TrojanPinata/Model-B/assets/keymap.png

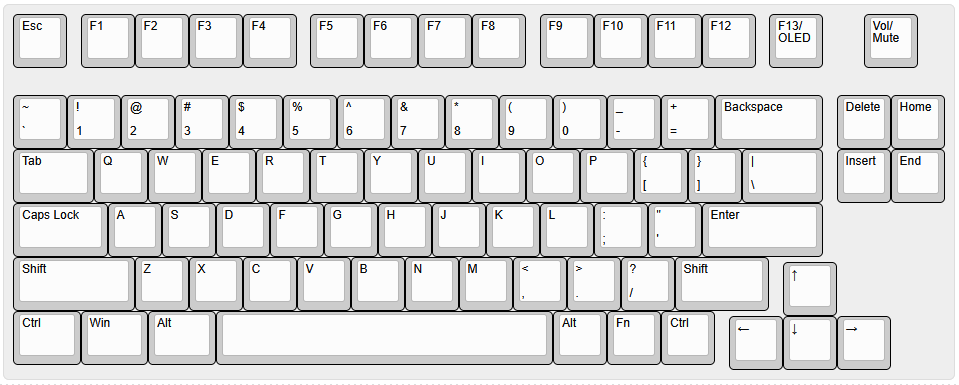
assets/keymap.png
