TrojanPinata/Model-B/assets/modelb.png

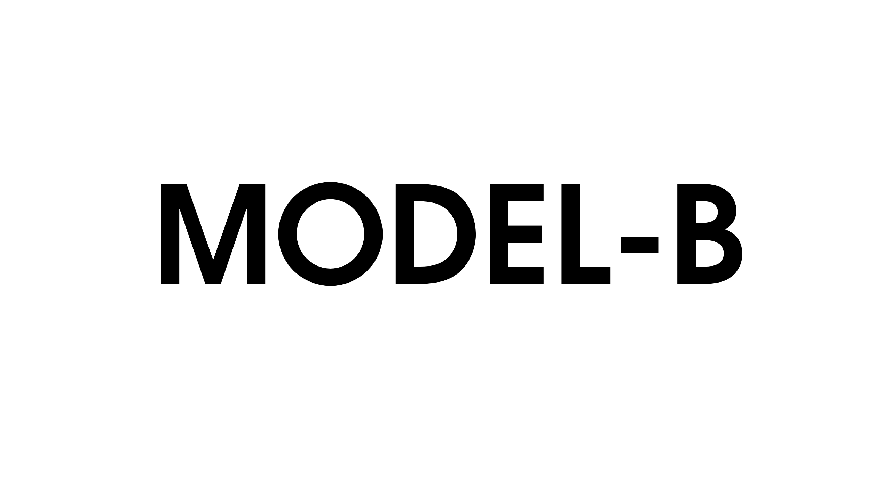
assets/modelb.png
