TrojanPinata/Model-B/case/blk.png

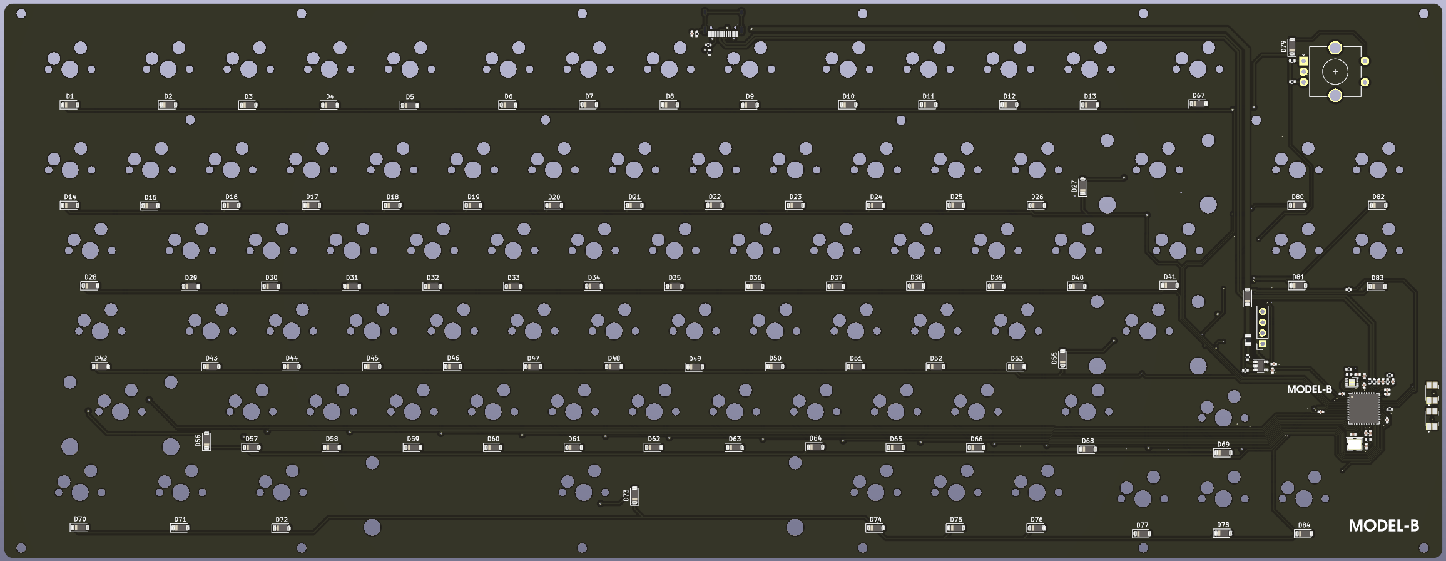
case/blk.png
