TrojanPinata/Model-B/case/blk_rear.png

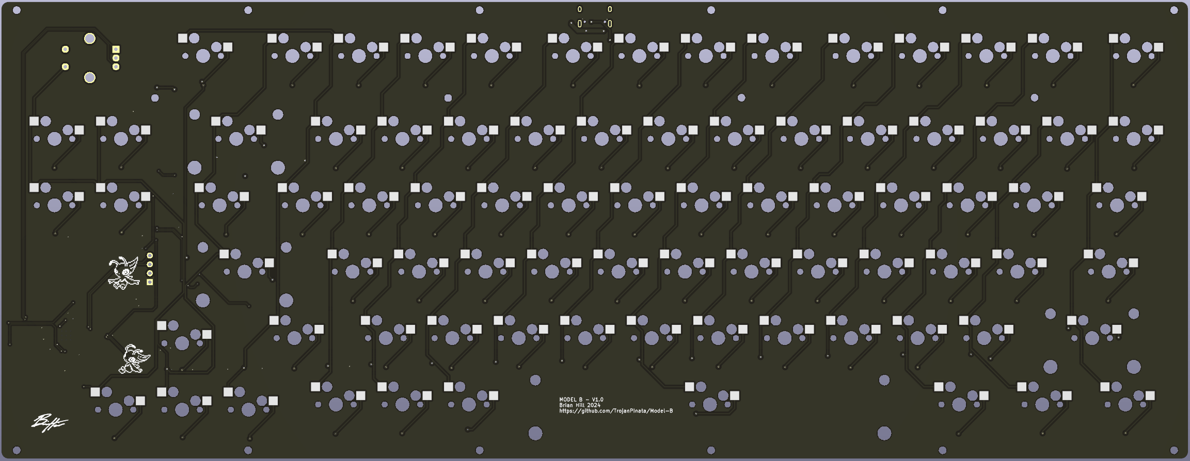
case/blk_rear.png
