TrojanPinata/Model-B/case/board.png

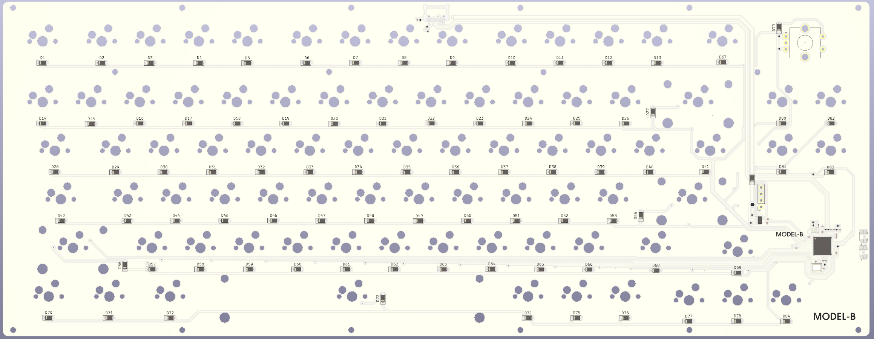
case/board.png
