TrojanPinata/Model-B/case/rear.png

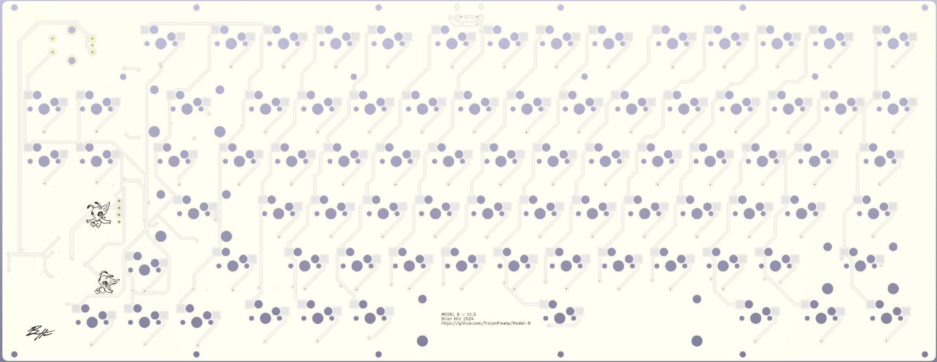
case/rear.png
