TrojanPinata/Model-B/case/ref-trans.png

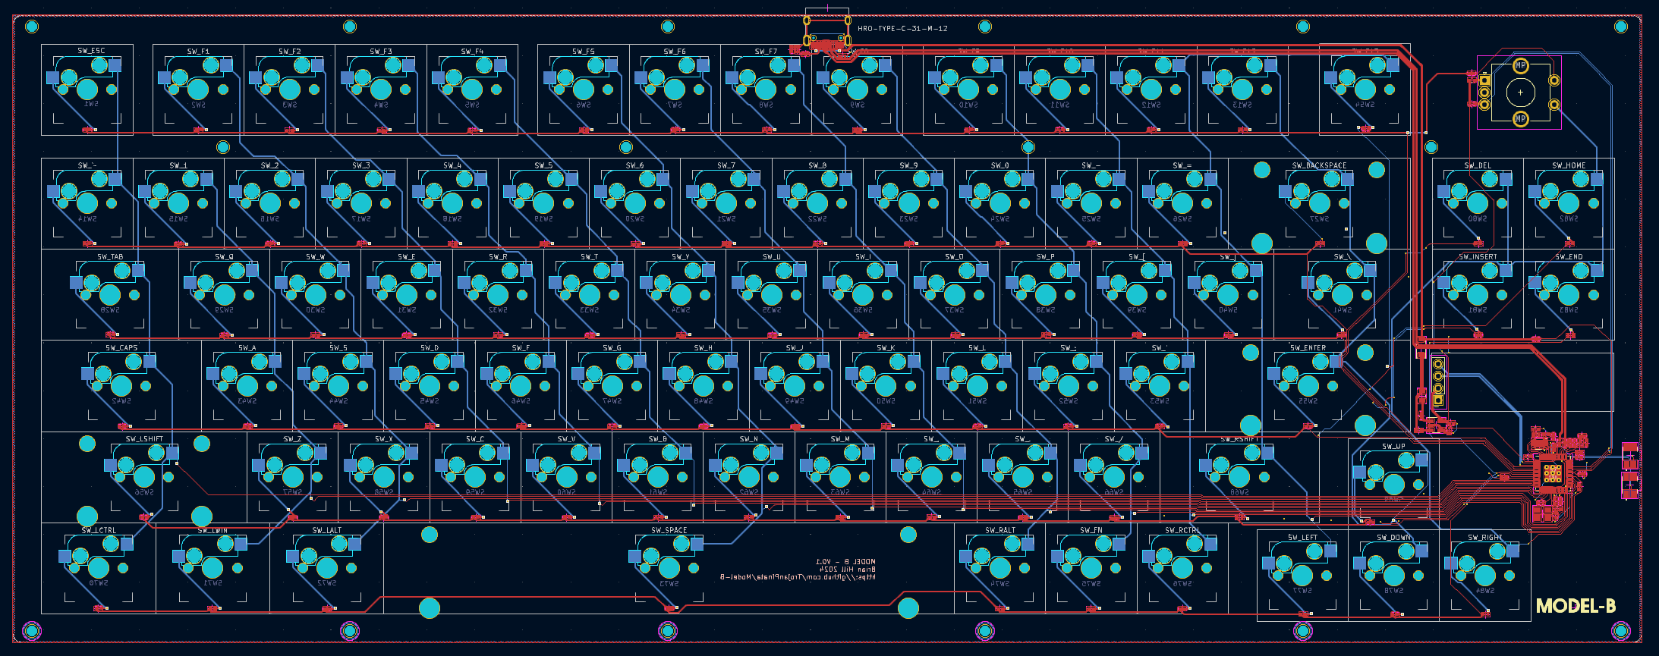
case/ref-trans.png
