TrojanPinata/Model-B/case/ref.png

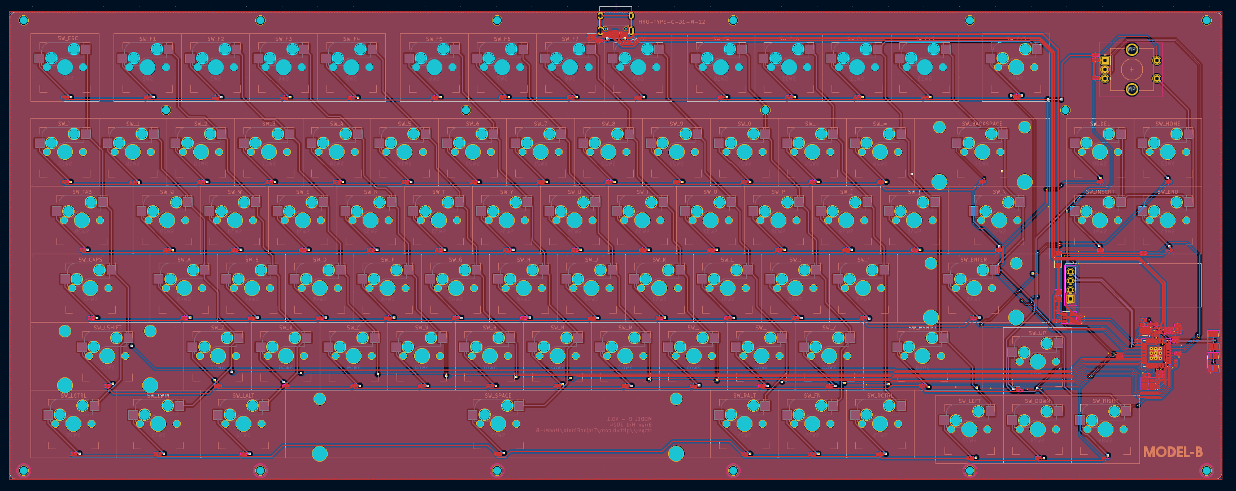
case/ref.png
