TrojanPinata/Model-B/case/renders/keyb2.png

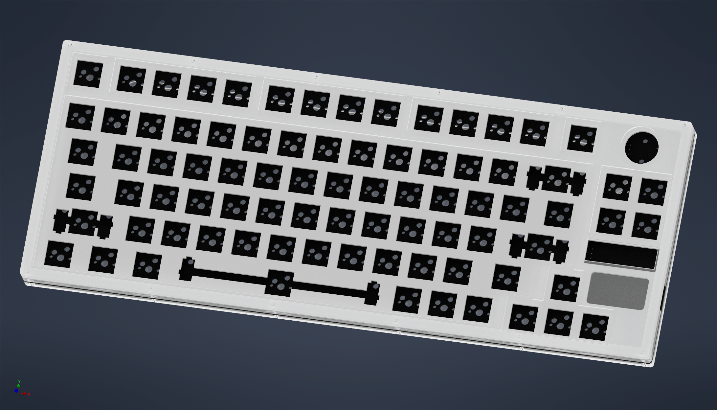
case/renders/keyb2.png
