TrojanPinata/Model-B/case/renders/keyb3.png

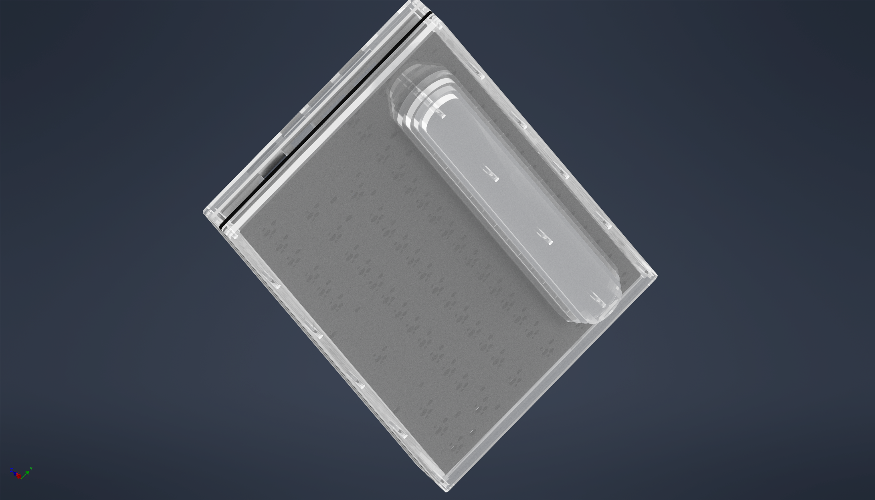
case/renders/keyb3.png
