TrojanPinata/Model-B/case/renders/keyb4.png

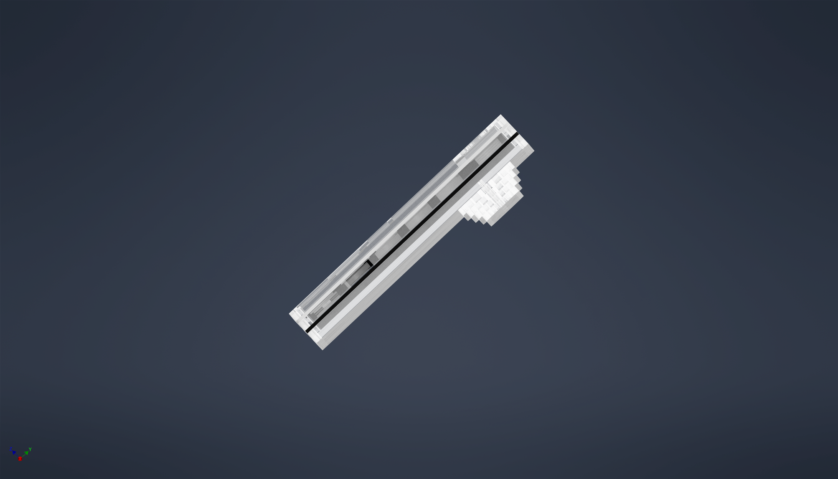
case/renders/keyb4.png
