TrojanPinata/Model-B/case/renders/keyb5.png

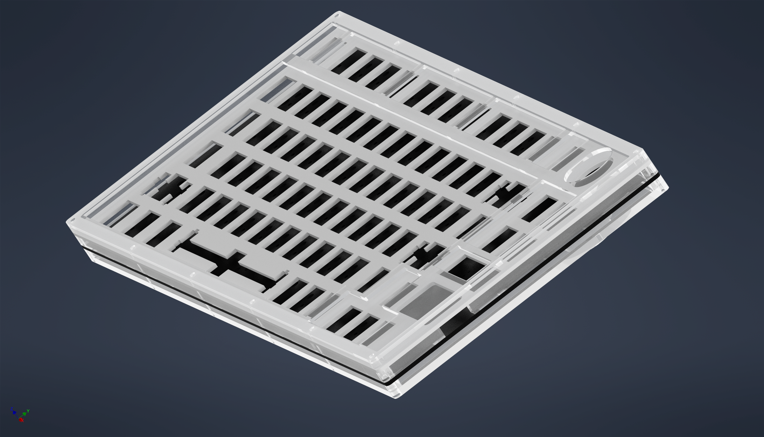
case/renders/keyb5.png
