TrojanPinata/Model-B/case/renders/keyb6.png

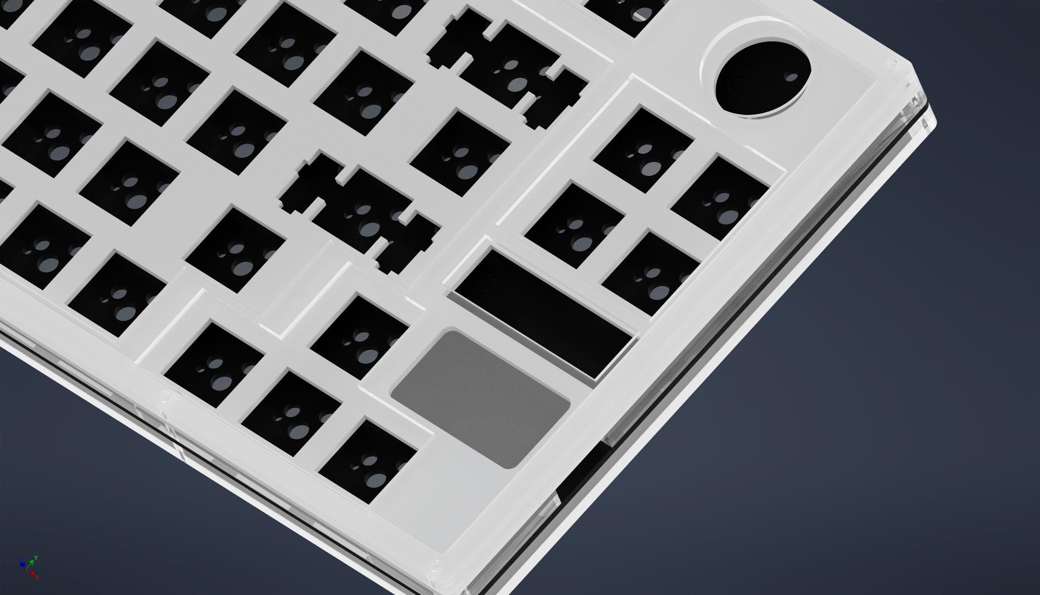
case/renders/keyb6.png
