TrojanPinata/Model-B/case/renders/keyb8.png

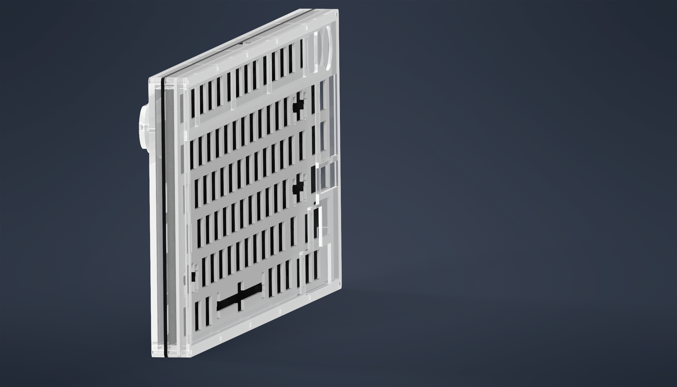
case/renders/keyb8.png
