TrojanPinata/Model-B/case/renders/keyb10.png

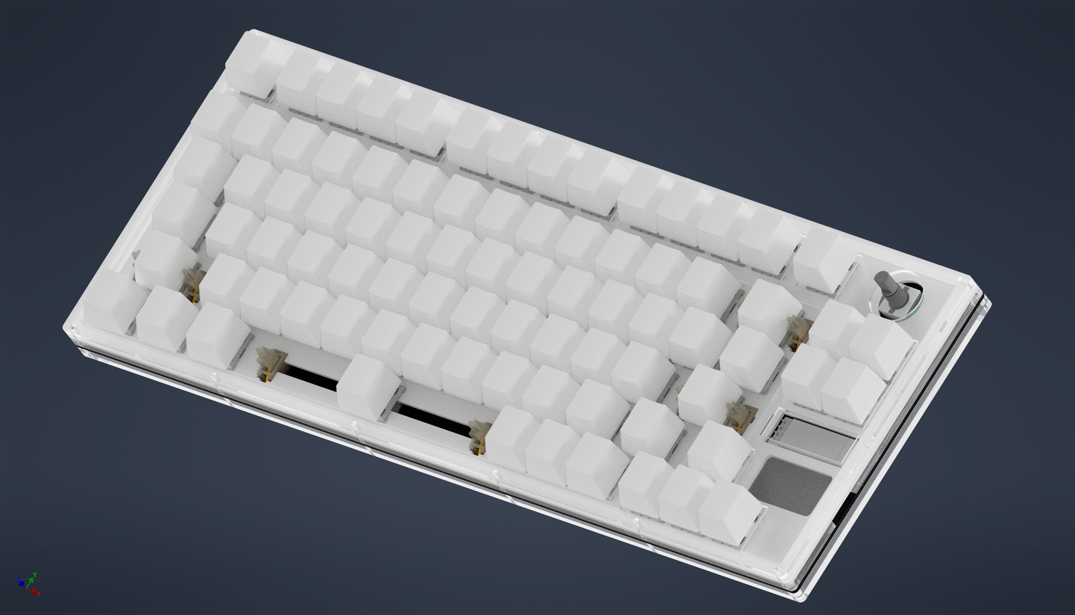
case/renders/keyb10.png
