TrojanPinata/Model-B/case/renders/keyb11.png

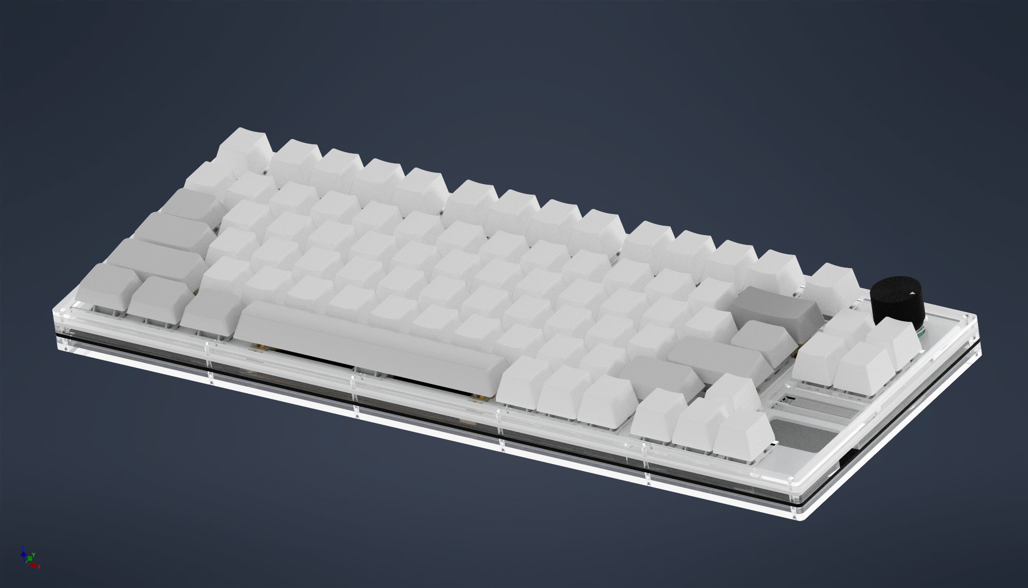
case/renders/keyb11.png
