TrojanPinata/Model-B/case/renders/keyb12.png

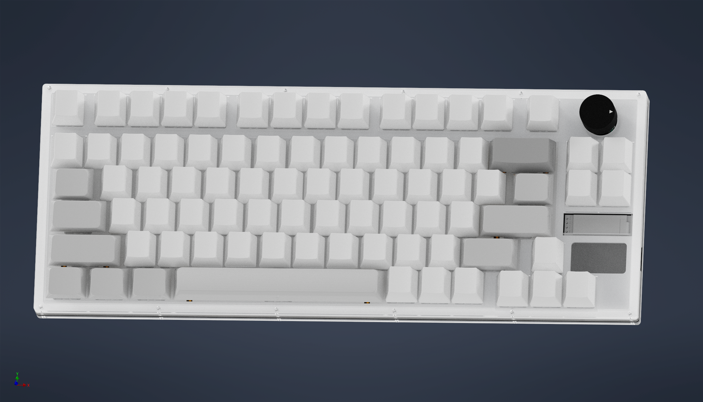
case/renders/keyb12.png
