TrojanPinata/Model-B/case/renders/keyb13.png

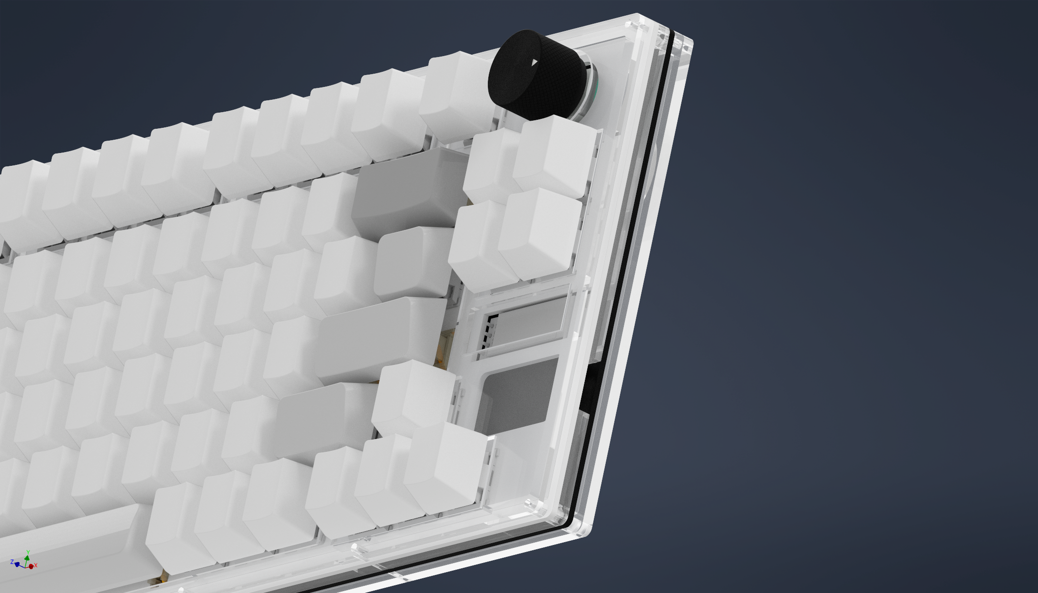
case/renders/keyb13.png
