TrojanPinata/Model-B/case/renders/keyb14.png

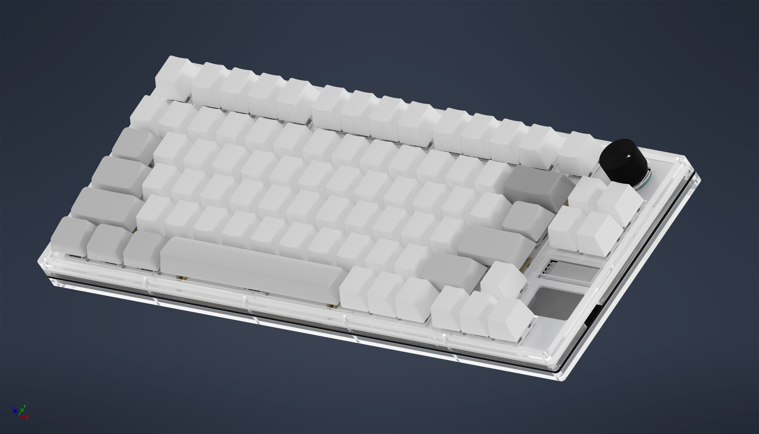
case/renders/keyb14.png
