TrojanPinata/Model-B/case/renders/keyb15.png

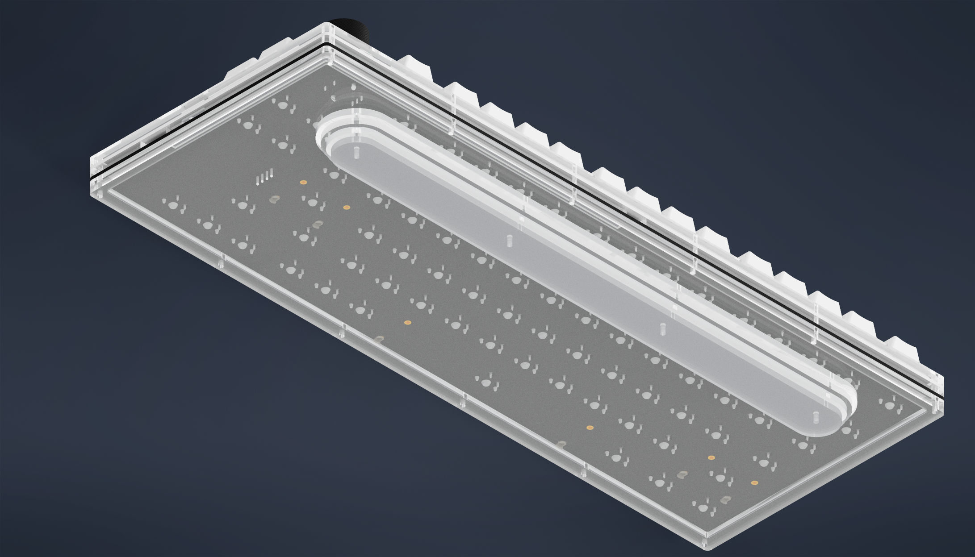
case/renders/keyb15.png
