TrojanPinata/Model-B/case/renders/keyb16.png

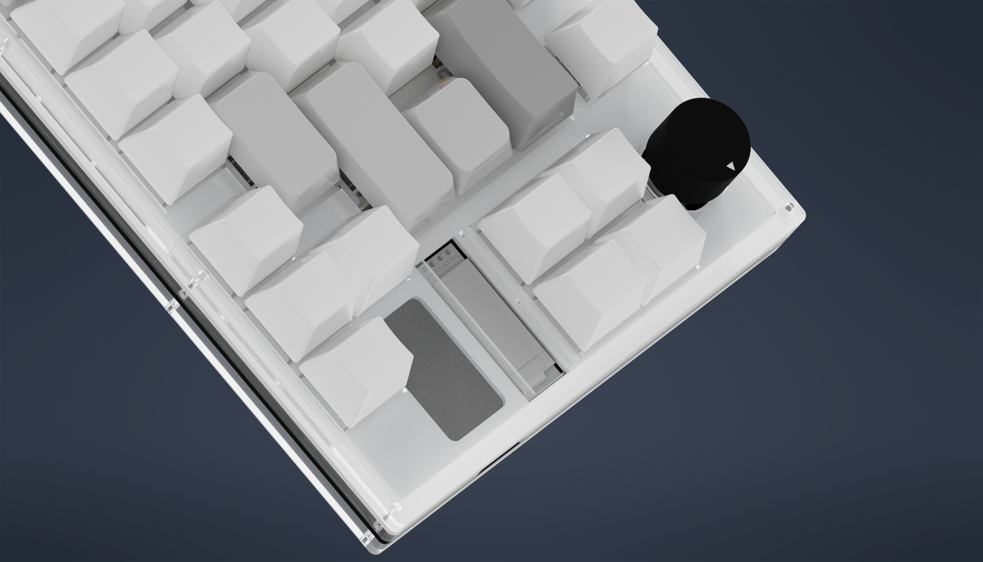
case/renders/keyb16.png
