TrojanPinata/Model-B/case/renders/keyb17.png

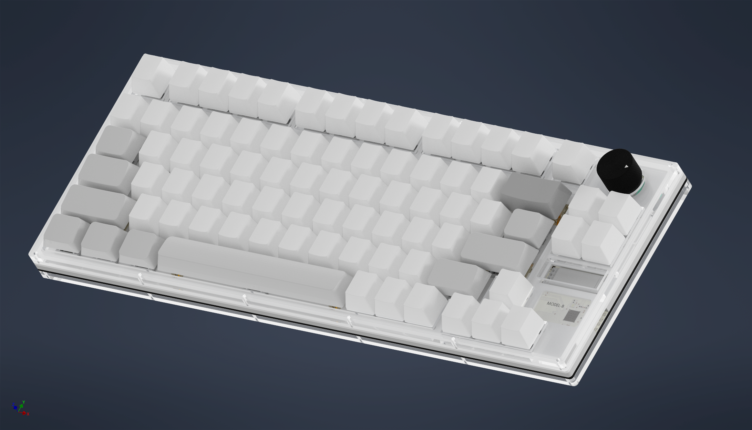
case/renders/keyb17.png
