TrojanPinata/Model-B/case/renders/keyb18.png

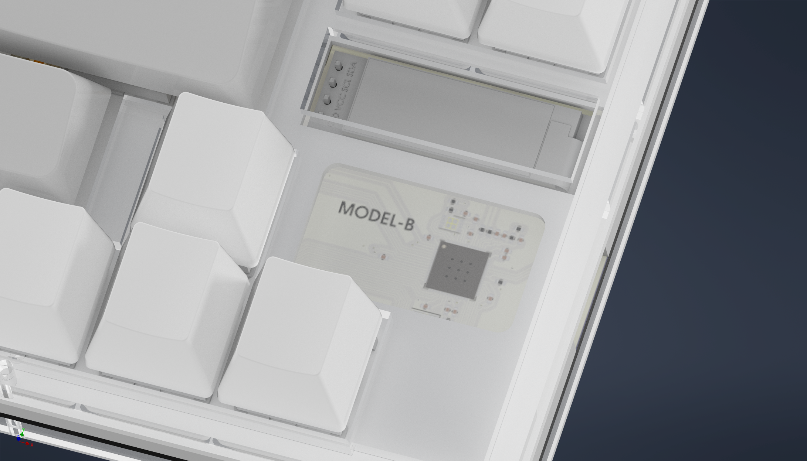
case/renders/keyb18.png
