TrojanPinata/Model-B/case/renders/keyb19.png

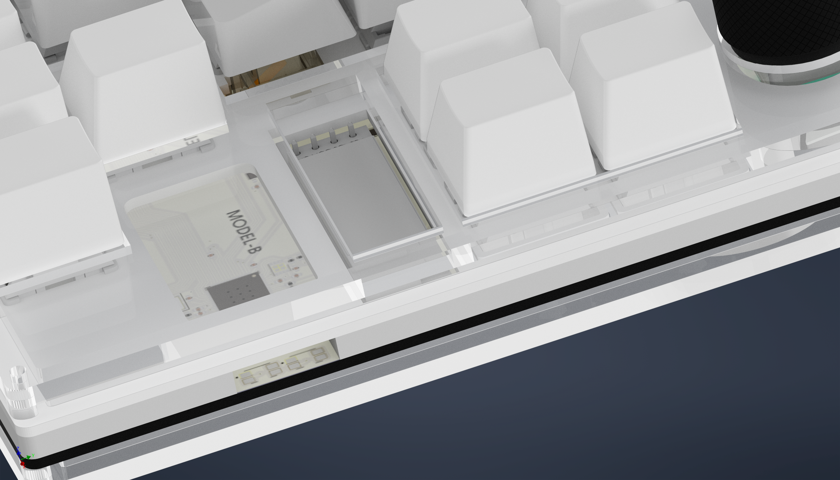
case/renders/keyb19.png
