TrojanPinata/Model-B/case/renders/keyb23.png

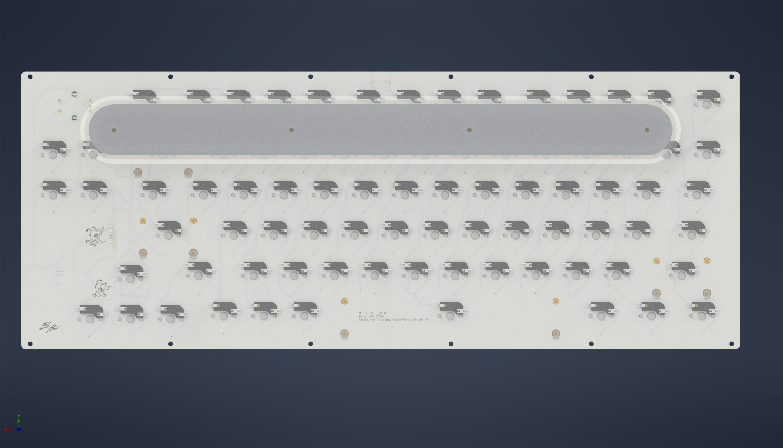
case/renders/keyb23.png
