TrojanPinata/Model-B/case/renders/keyb24.png

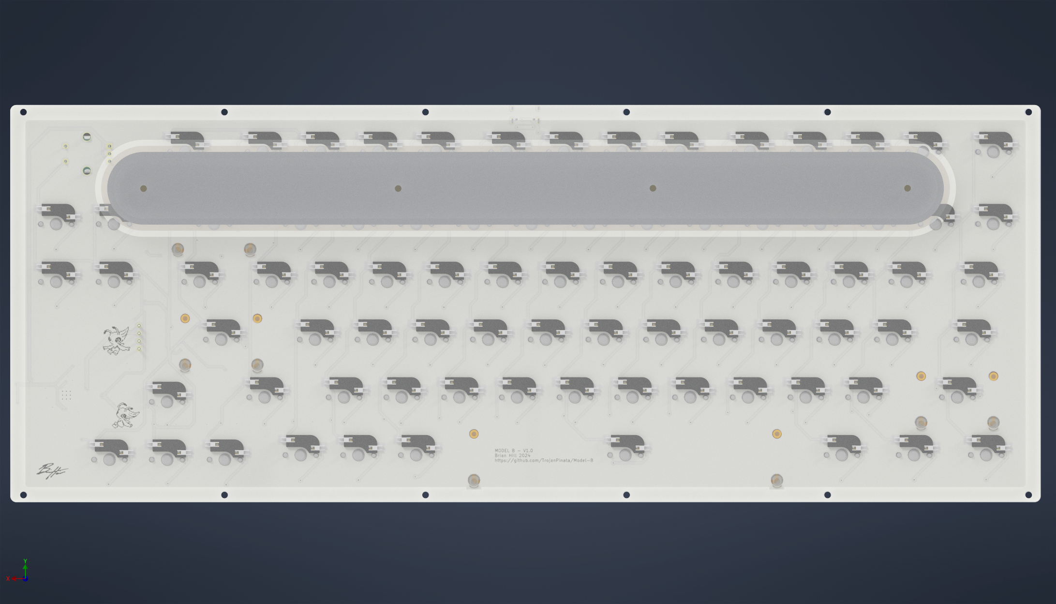
case/renders/keyb24.png
