TrojanPinata/Model-B/case/renders/keyb25.png

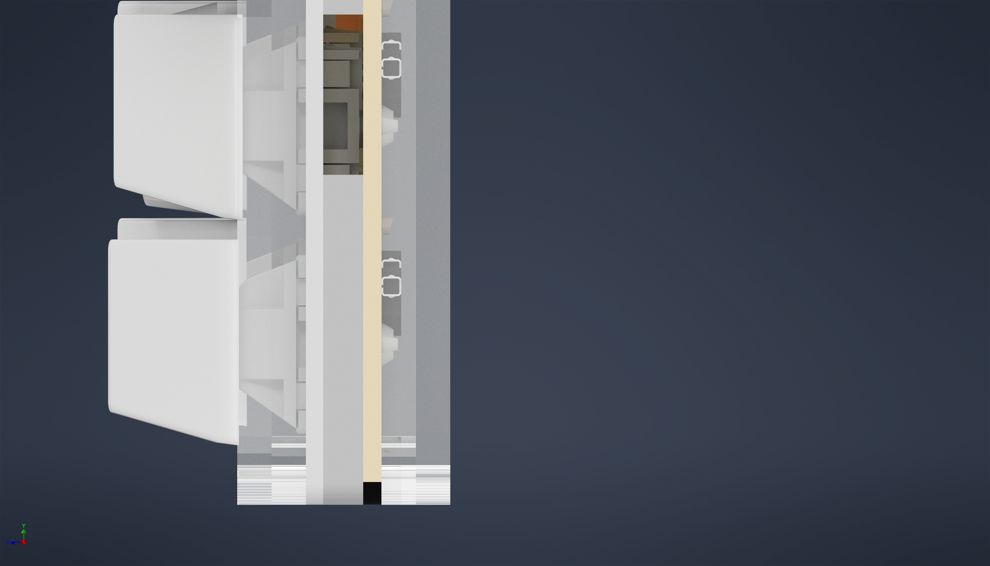
case/renders/keyb25.png
