TrojanPinata/Model-B/case/renders/keyb26.png

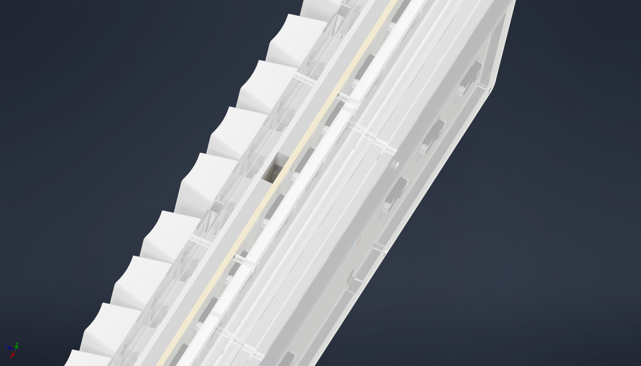
case/renders/keyb26.png
