TrojanPinata/Model-B/case/renders/keyb27.png

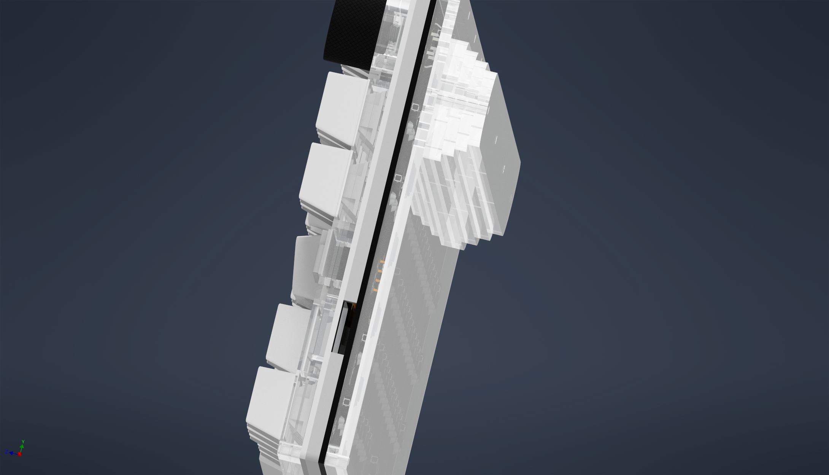
case/renders/keyb27.png
