TrojanPinata/Model-B/case/renders/keyb28.png

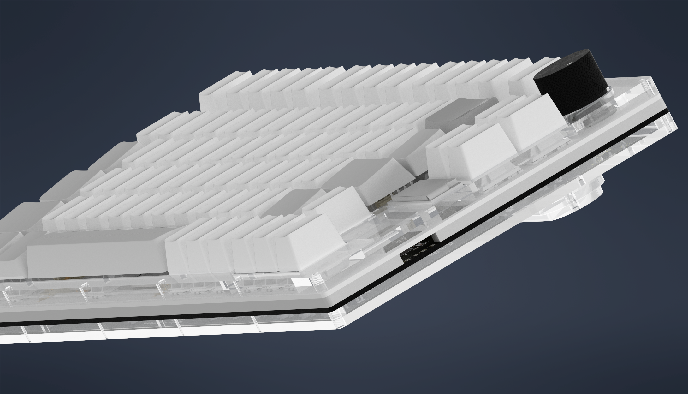
case/renders/keyb28.png
