TrojanPinata/Model-B/case/renders/keyb29.png

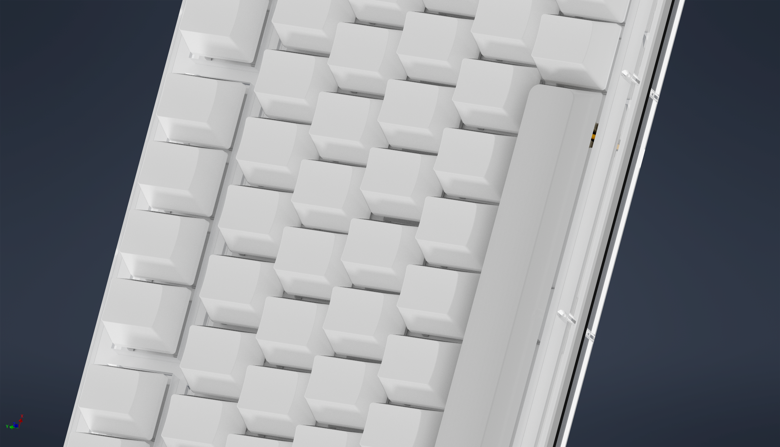
case/renders/keyb29.png
