TrojanPinata/Model-B/case/renders/keyb30.png

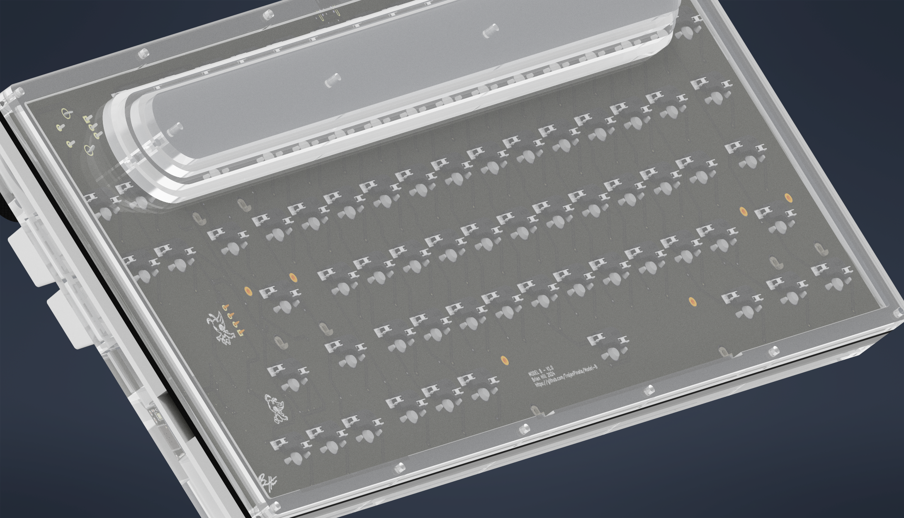
case/renders/keyb30.png
