TrojanPinata/Model-B/case/renders/keyb31.png

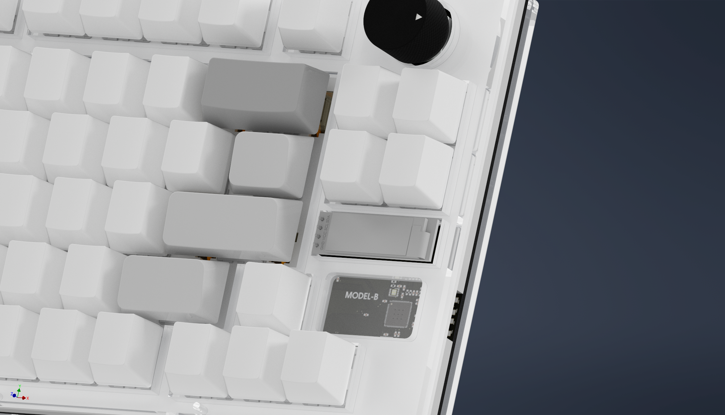
case/renders/keyb31.png
