TrojanPinata/Model-B/case/renders/keyb32.png

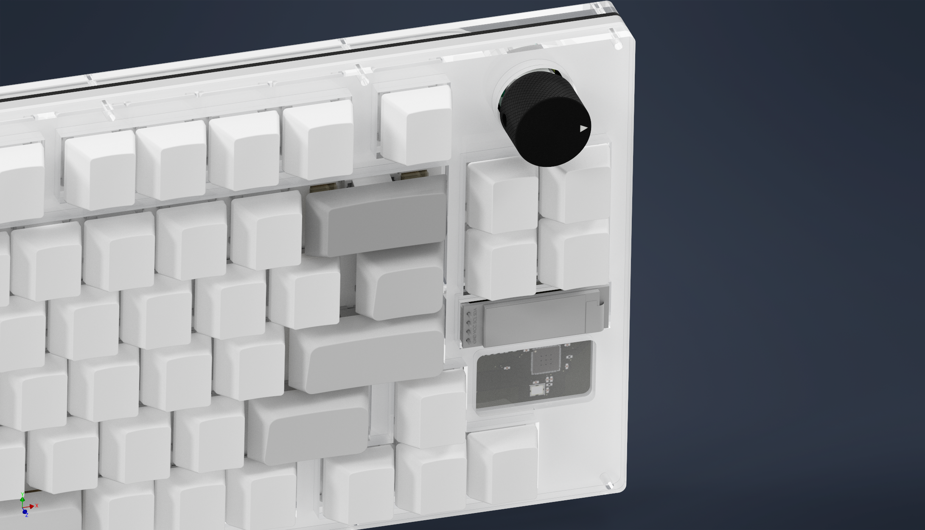
case/renders/keyb32.png
