TrojanPinata/Model-B/case/renders/keyb33.png

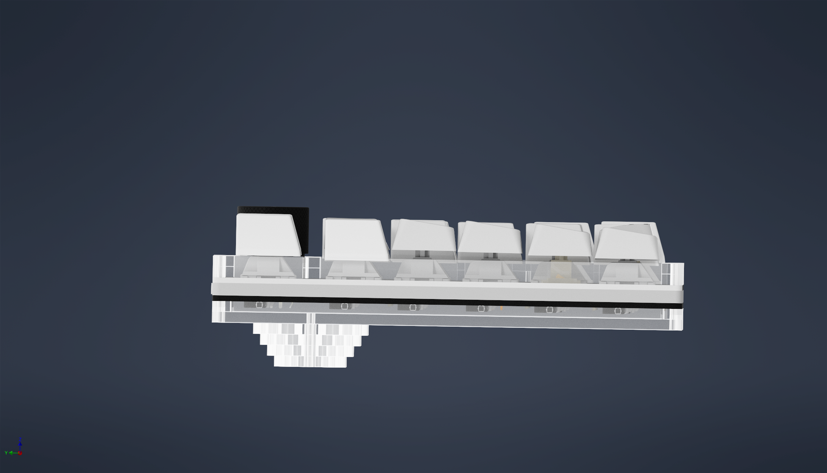
case/renders/keyb33.png
