TrojanPinata/Model-B/case/renders/keyb34.png

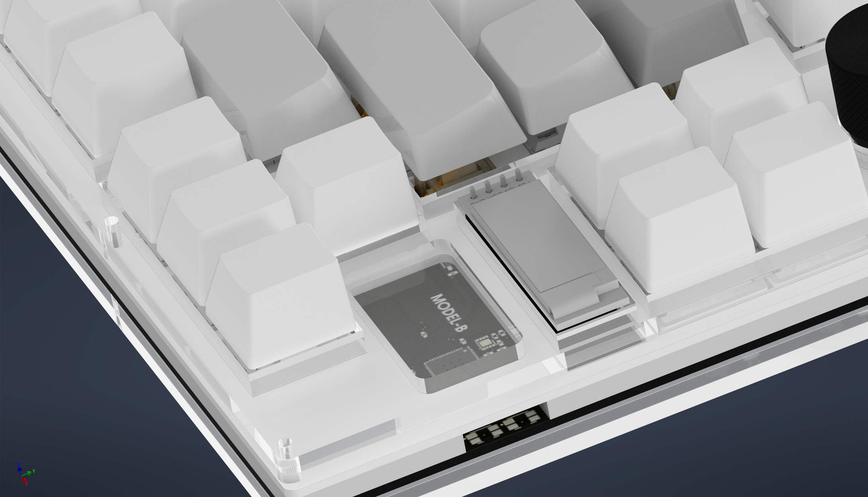
case/renders/keyb34.png
