TrojanPinata/Model-B/pcb/model-b/pcb_layout.png

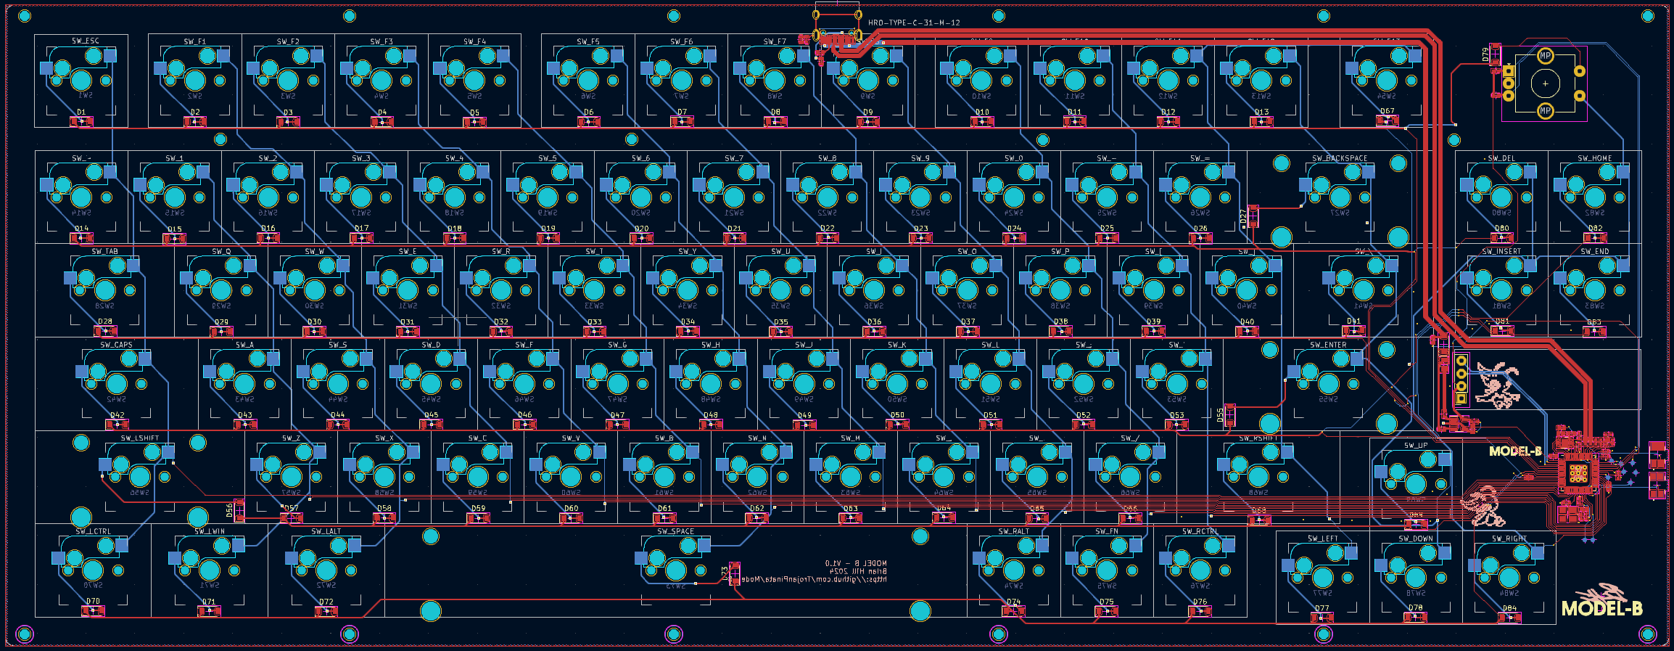
pcb/model-b/pcb_layout.png
