TrojanPinata/Model-B/case/models/references/POS_2u_Cherry_row1.stl

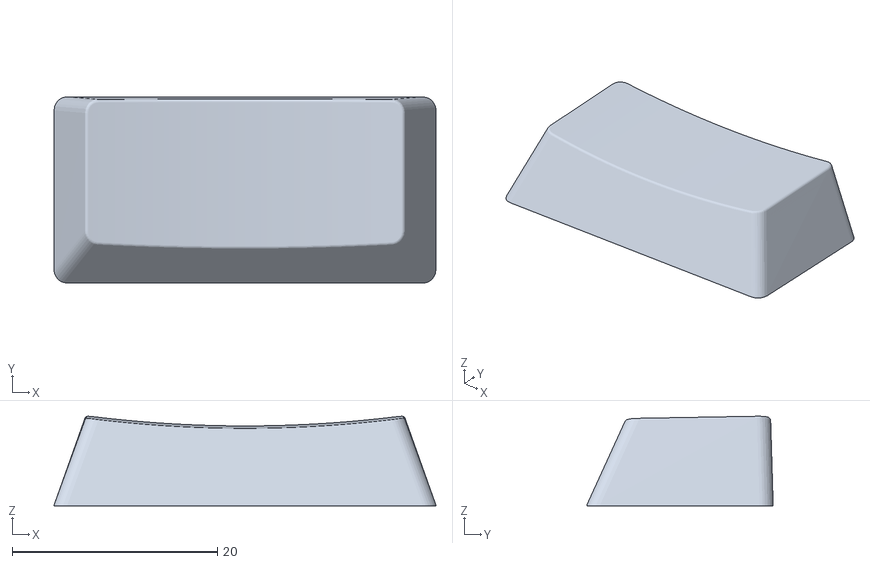
[picture p58: CAD file, 2024-07-27]
case/models/references/POS_2u_Cherry_row1.stl
37.2 x 18.2 x 8.72
