TrojanPinata/Model-B/case/exports/stp/toplayer-f1-f3.stp

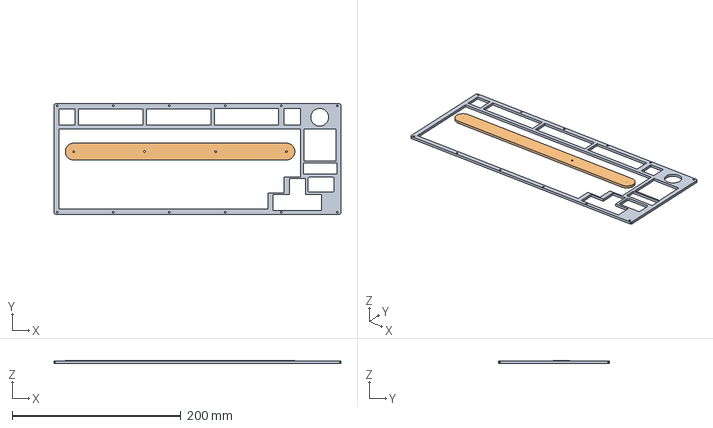
[picture p59: CAD file, 2024-09-26]
case/exports/stp/toplayer-f1-f3.stp
340.0 x 131.0 x 3.05 mm
top_plate PCB
foot4
