TrojanPinata/Model-B/case/exports/stp/open_layer_combiner.stp

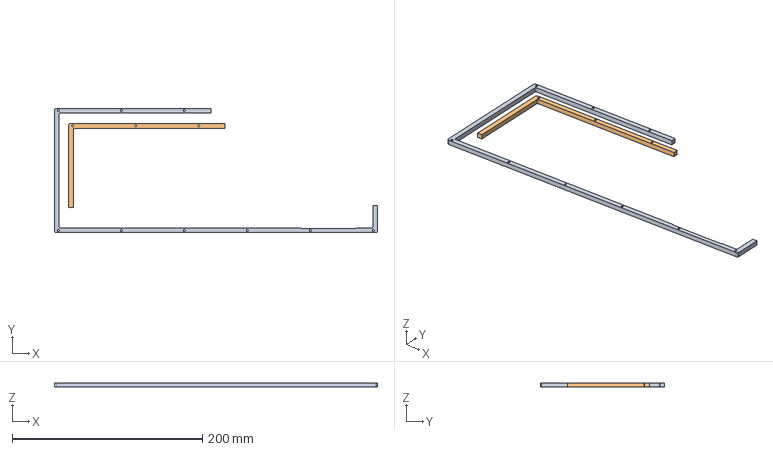
[picture p60: CAD file, 2024-07-27]
case/exports/stp/open_layer_combiner.stp
340.0 x 131.0 x 4.50 mm
open_liner_L
open_liner_S_MIR
