TrojanPinata/Model-B/case/exports/stp/window.stp

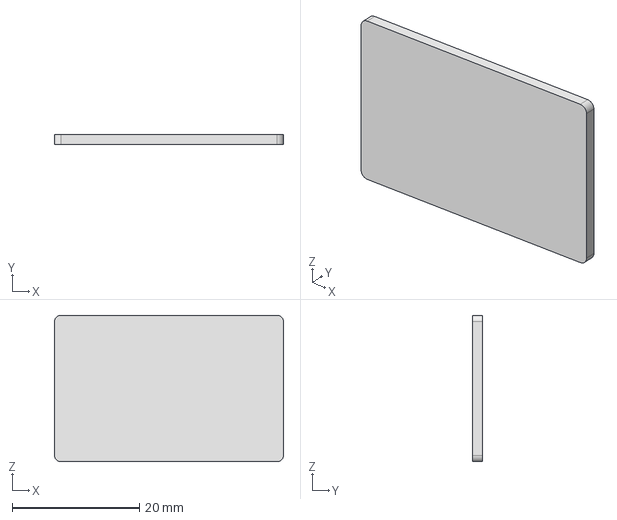
[picture p61: CAD file, 2024-07-07]
case/exports/stp/window.stp
36.0 x 1.50 x 23.0 mm
