TrojanPinata/Model-B/case/exports/stp/foot1.stp

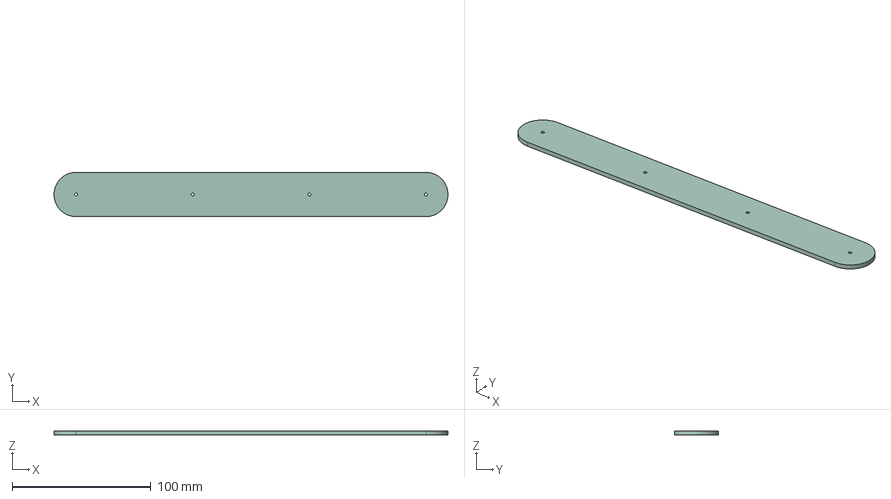
[picture p62: CAD file, 2024-07-05]
case/exports/stp/foot1.stp
284.1 x 32.0 x 3.00 mm
