TrojanPinata/Model-B/case/exports/stp/top-layer.stp

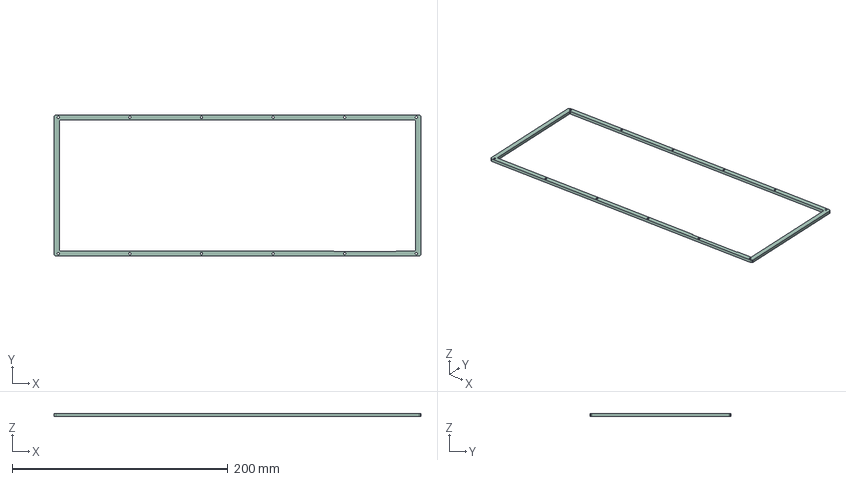
[picture p63: CAD file, 2024-07-05]
case/exports/stp/top-layer.stp
340.0 x 131.0 x 3.00 mm
