TrojanPinata/Model-B/case/exports/stp/foot3.stp

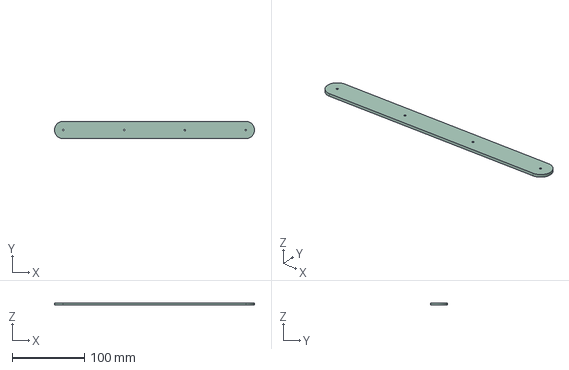
[picture p64: CAD file, 2024-07-05]
case/exports/stp/foot3.stp
276.1 x 24.0 x 3.00 mm
