TrojanPinata/Model-B/case/exports/stp/foot2.stp

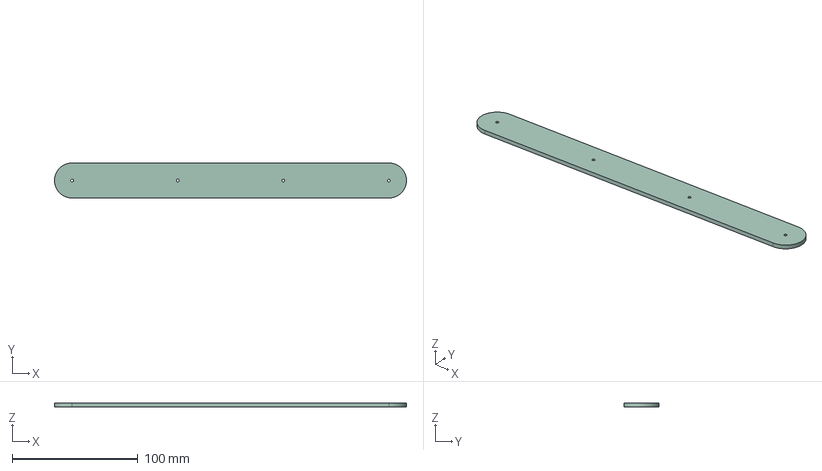
[picture p65: CAD file, 2024-07-05]
case/exports/stp/foot2.stp
280.1 x 28.0 x 3.00 mm
