TrojanPinata/Model-B/case/exports/stp/foot4.stp

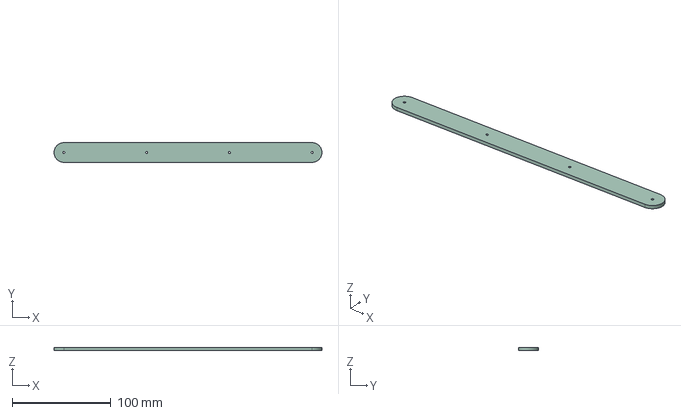
[picture p66: CAD file, 2024-07-05]
case/exports/stp/foot4.stp
272.1 x 20.0 x 3.00 mm
